Banjer21/DIY-HOTAS/Joystick/Righthanded Updated/Gimbal/Xaxis Arm V2 [B21] [ADD].stl

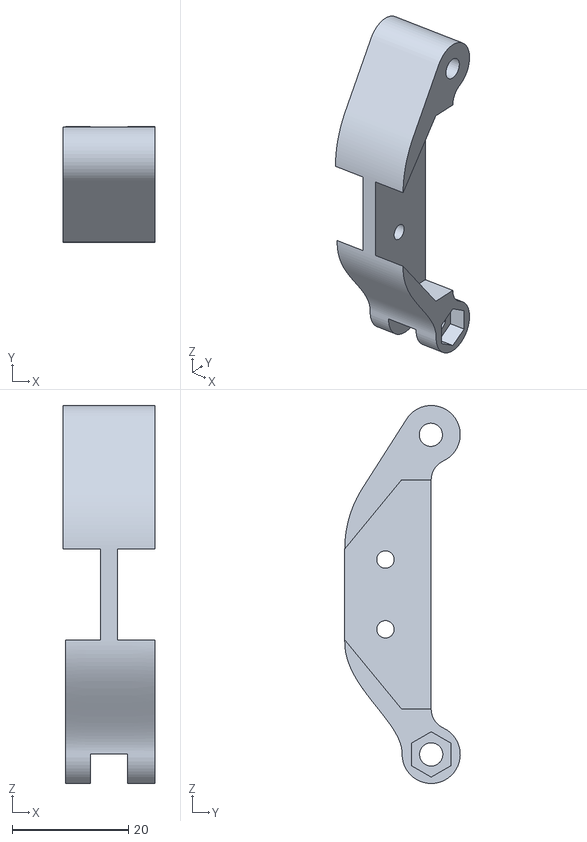
[picture p15: CAD file, 2025-05-15]
Joystick/Righthanded Updated/Gimbal/Xaxis Arm V2 [B21] [ADD].stl
15.8 x 19.9 x 65.0
