Banjer21/DIY-HOTAS/Joystick/Righthanded Updated/Head/Toggle Switch Housing V3 [B21] [ADD].stl

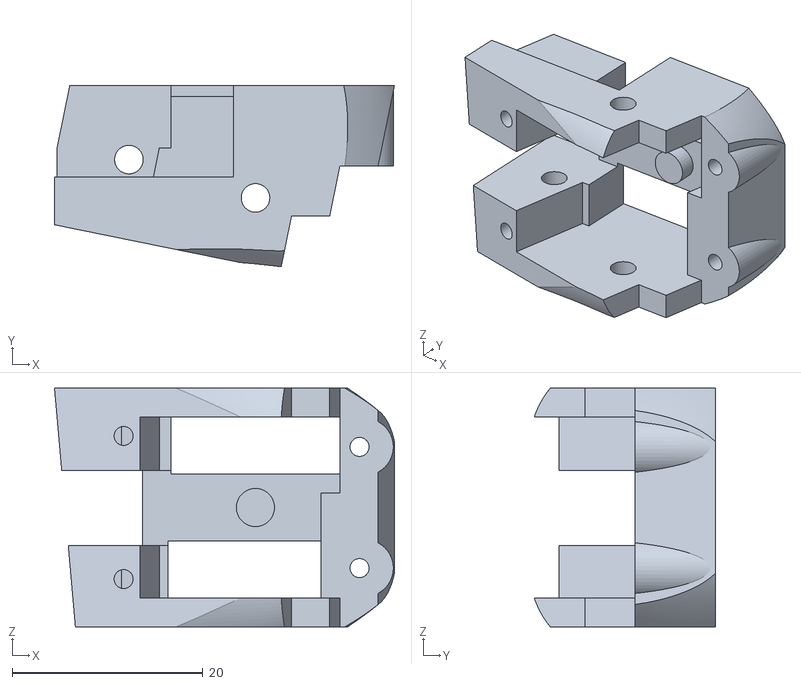
[picture p16: CAD file, 2025-05-15]
Joystick/Righthanded Updated/Head/Toggle Switch Housing V3 [B21] [ADD].stl
35.6 x 19.0 x 25.0
