Banjer21/DIY-HOTAS/Throttle/ThrottleBase Deskmount.step

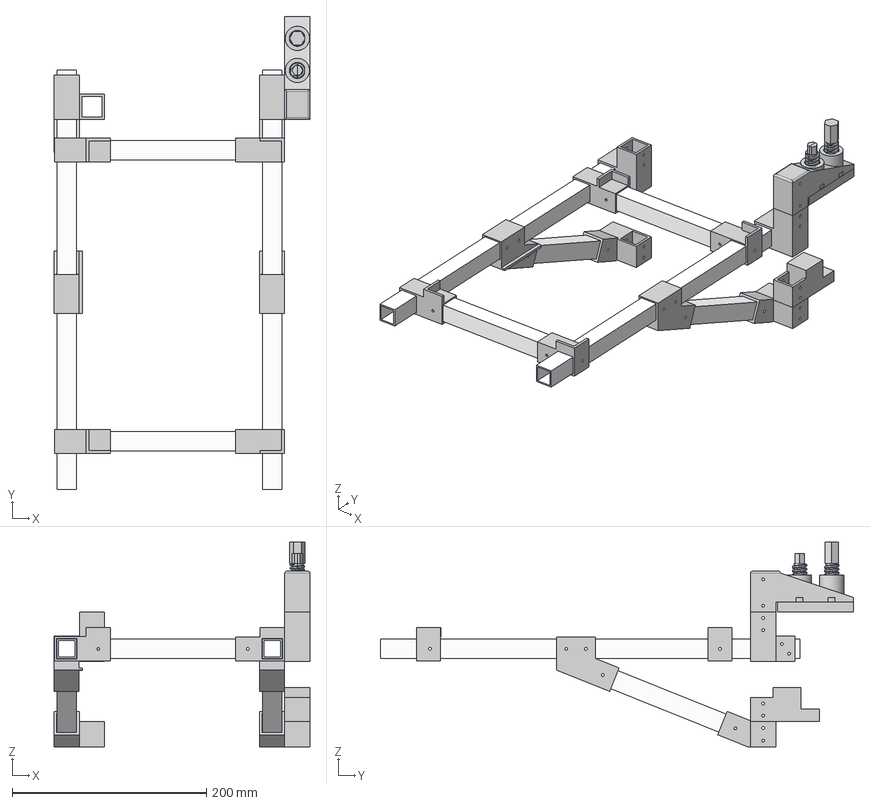
[picture p17: CAD file, 2025-04-23]
Throttle/ThrottleBase Deskmount.step
263.5 x 486.9 x 211.0 mm
