Banjer21/DIY-HOTAS/XY-stage.step

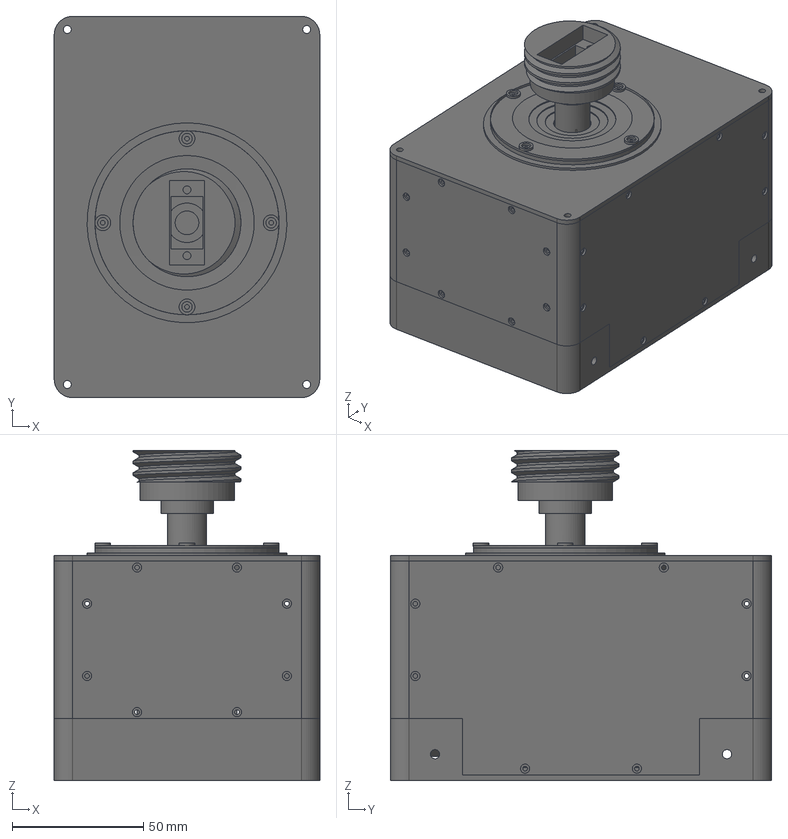
[picture p18: CAD file, 2025-02-13]
XY-stage.step
101.0 x 145.0 x 125.5 mm
Axle (2)
Xaxis resistive Right (1)
Xaxis Cariage Right (1)
MainFrame Right (1)
Yaxis resistive Right (1)
Case Right (1)
