Banjer21/DIY-HOTAS/Joystick/Righthanded joystick/Body/break lever.stl

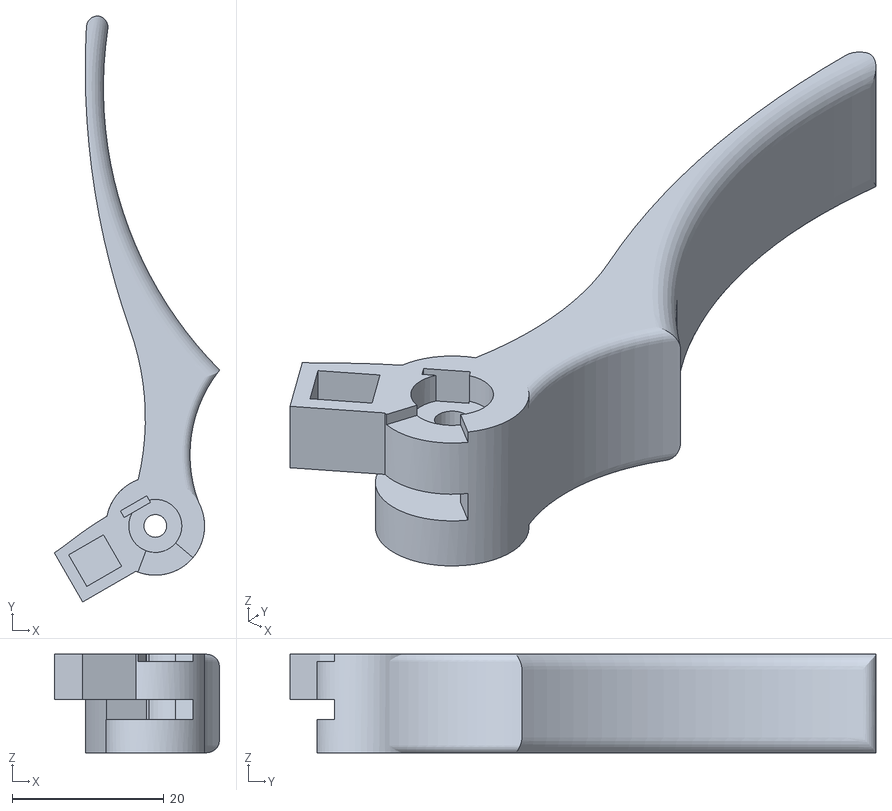
[picture p19: CAD file, 2025-03-08]
Joystick/Righthanded joystick/Body/break lever.stl
21.8 x 77.2 x 13.0
