Banjer21/DIY-HOTAS/Joystick/Righthanded joystick/Buttons/HS Top.stl

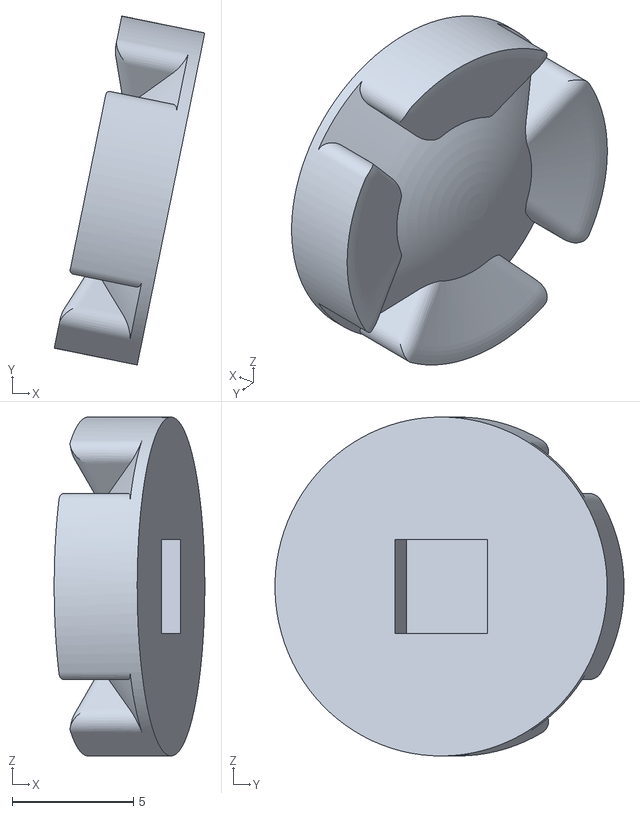
[picture p20: CAD file, 2025-03-08]
Joystick/Righthanded joystick/Buttons/HS Top.stl
6.22 x 14.4 x 14.0
