Banjer21/DIY-HOTAS/Joystick/Righthanded joystick/Gimbal/CoverPlate.stl

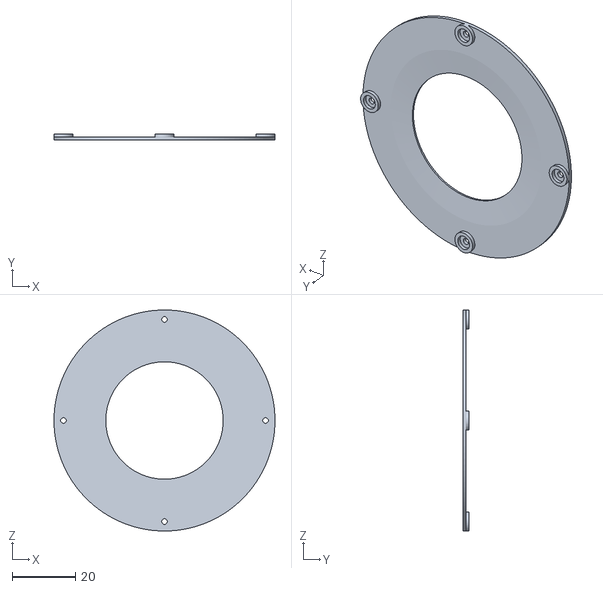
[picture p21: CAD file, 2025-03-08]
Joystick/Righthanded joystick/Gimbal/CoverPlate.stl
70.0 x 2.00 x 70.0
