Banjer21/DIY-HOTAS/Joystick/Righthanded joystick/Gimbal/GimbalCase/Lid.stl

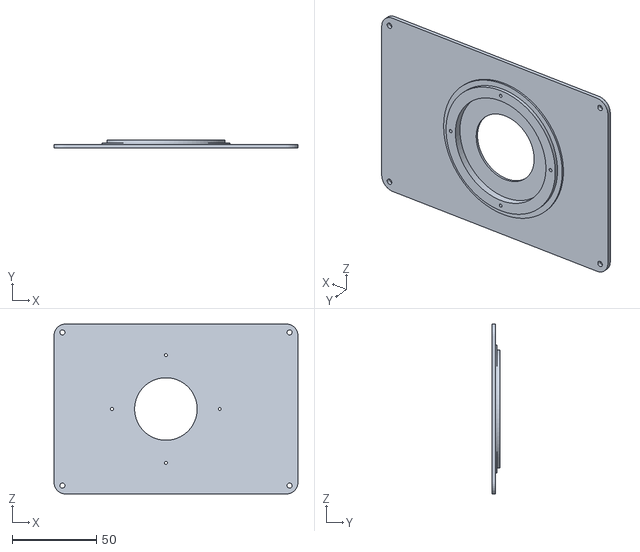
[picture p22: CAD file, 2025-03-08]
Joystick/Righthanded joystick/Gimbal/GimbalCase/Lid.stl
145.0 x 4.85 x 101.0
