Banjer21/DIY-HOTAS/Joystick/Righthanded joystick/Head/SecondTriggerHousing.stl

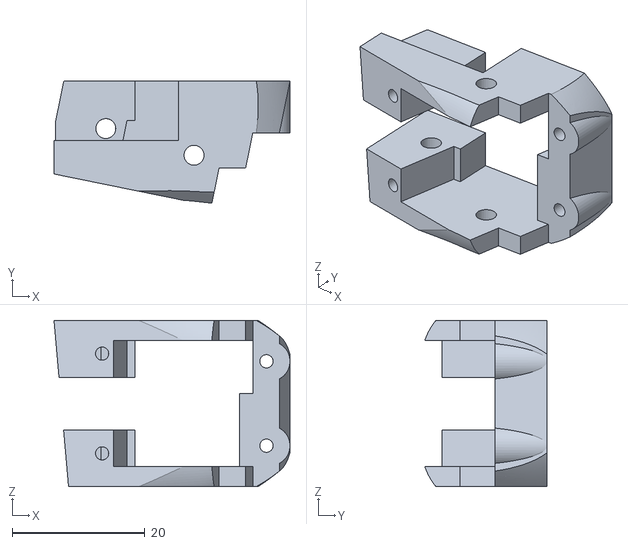
[picture p23: CAD file, 2025-03-08]
Joystick/Righthanded joystick/Head/SecondTriggerHousing.stl
35.5 x 18.4 x 25.0
