Banjer21/DIY-HOTAS/Joystick/Righthanded joystick/Zaxis/Zaxis topMag.stl

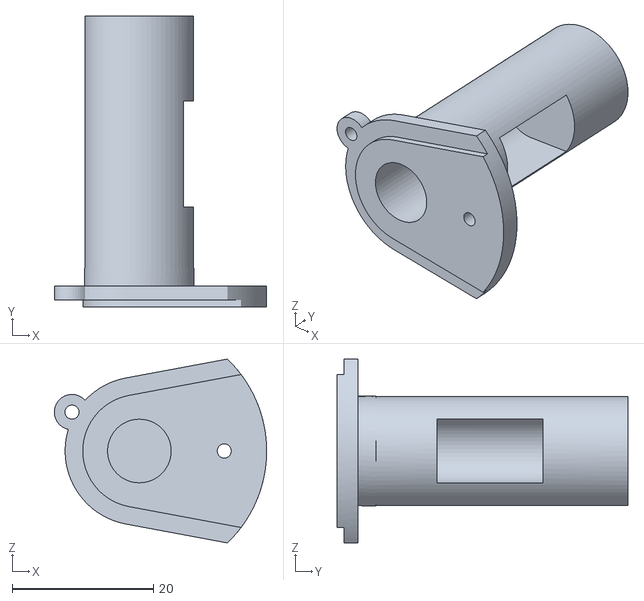
[picture p24: CAD file, 2025-03-08]
Joystick/Righthanded joystick/Zaxis/Zaxis topMag.stl
30.0 x 41.1 x 26.0
