Banjer21/DIY-HOTAS/Joystick/Righthanded Updated/Body/Brake Lever [B21] [ADD].stl

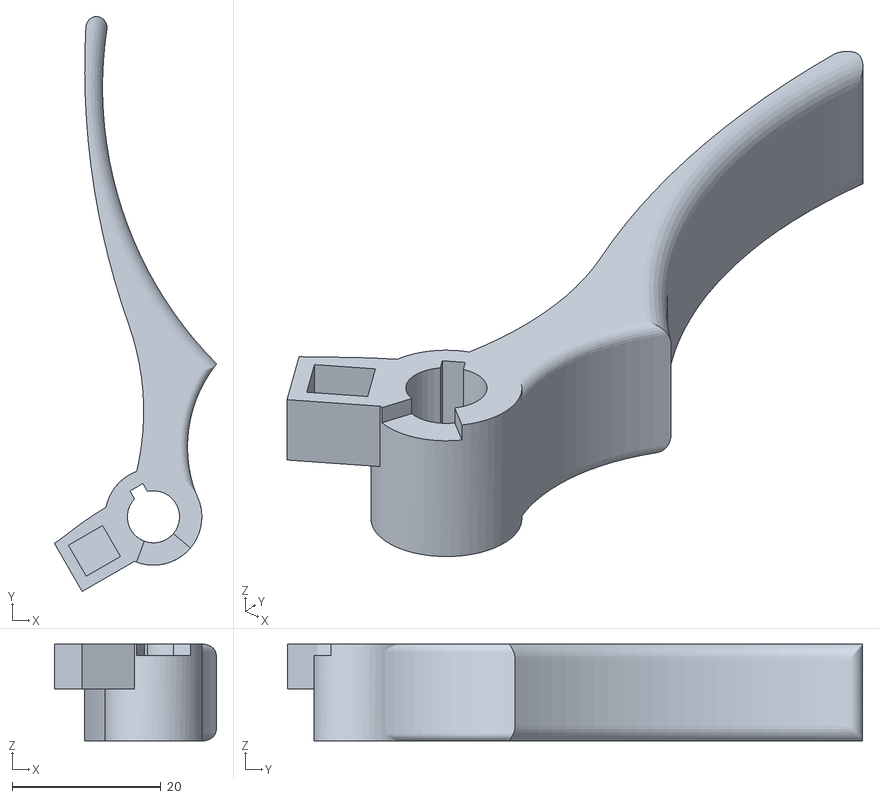
[picture p25: CAD file, 2025-05-15]
Joystick/Righthanded Updated/Body/Brake Lever [B21] [ADD].stl
21.8 x 77.2 x 13.0
