Banjer21/DIY-HOTAS/Joystick/Righthanded Updated/Head/Top Extended [B21].stl

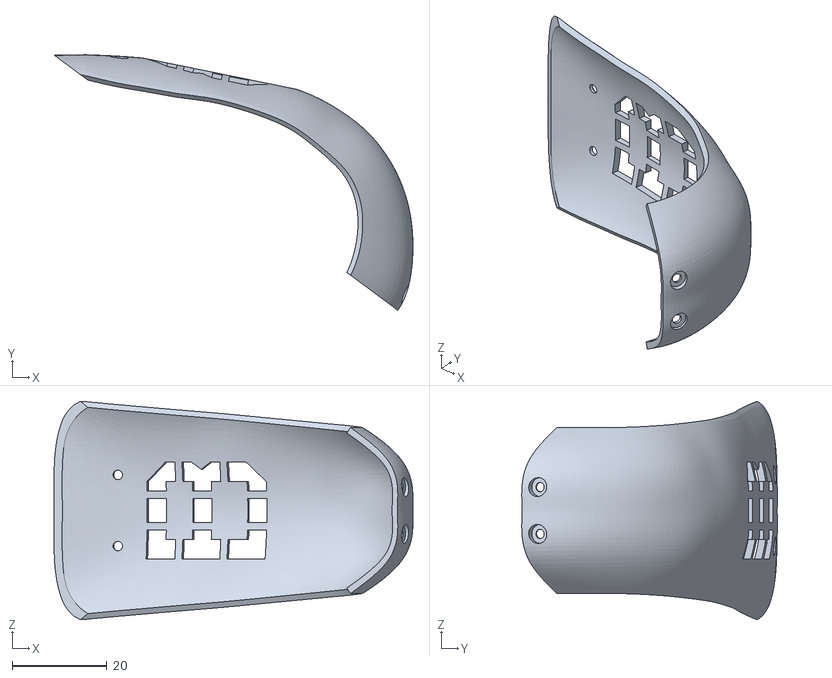
[picture p26: CAD file, 2025-05-15]
Joystick/Righthanded Updated/Head/Top Extended [B21].stl
75.7 x 53.9 x 46.1
