Banjer21/DIY-HOTAS/Joystick/Righthanded joystick/Buttons/Button.stl

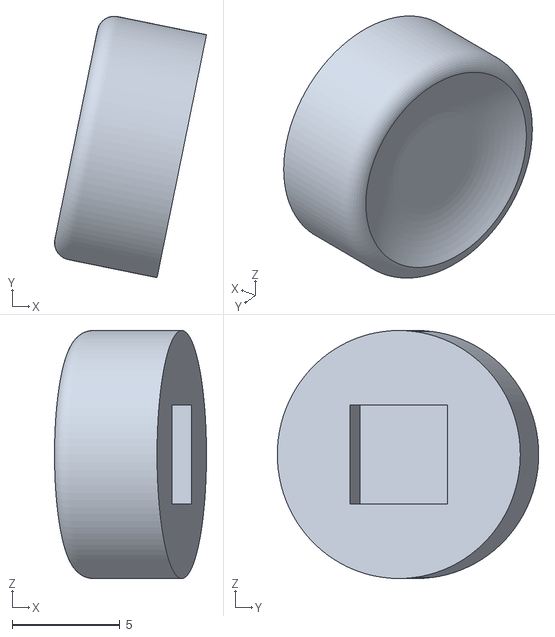
[picture p27: CAD file, 2025-03-08]
Joystick/Righthanded joystick/Buttons/Button.stl
7.05 x 12.1 x 11.5
