Banjer21/DIY-HOTAS/Joystick/Righthanded joystick/Gimbal/GimbalCase/BottomMCP.stl

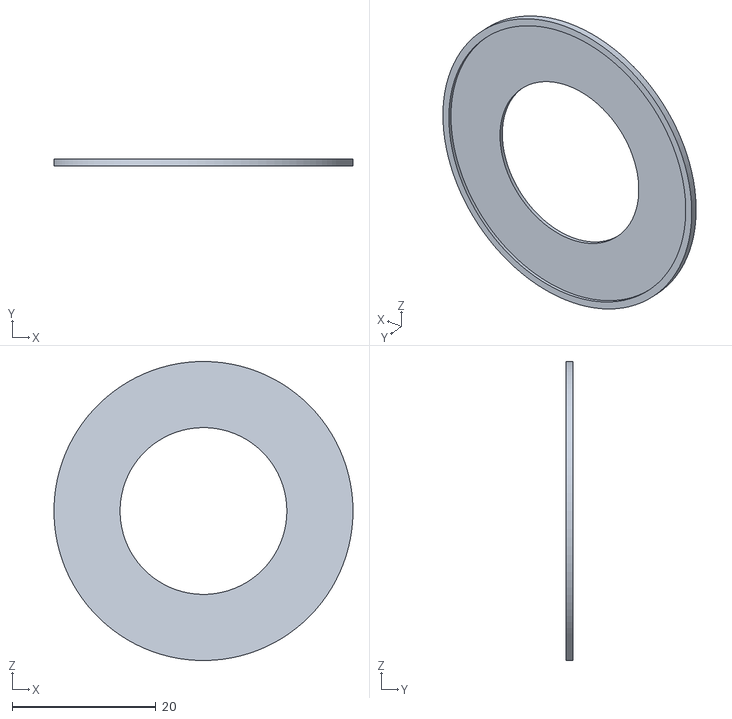
[picture p28: CAD file, 2025-03-08]
Joystick/Righthanded joystick/Gimbal/GimbalCase/BottomMCP.stl
41.6 x 0.95 x 41.6
