Banjer21/DIY-HOTAS/Joystick/Righthanded joystick/Head/Front Button Panel.stl

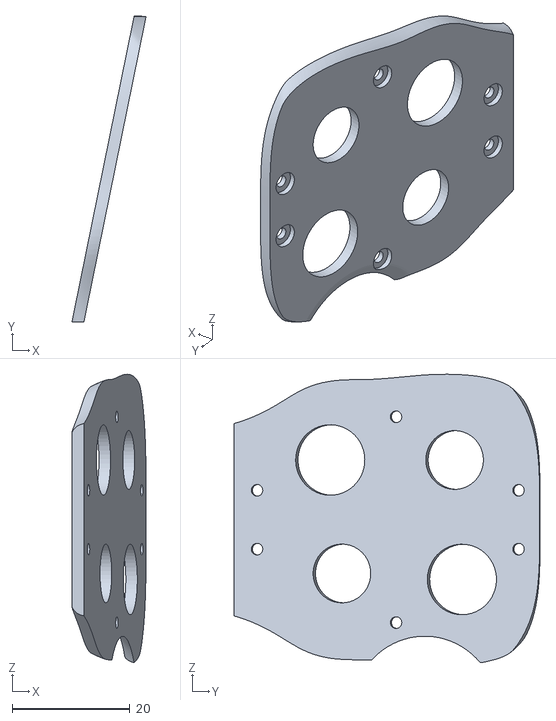
[picture p29: CAD file, 2025-03-08]
Joystick/Righthanded joystick/Head/Front Button Panel.stl
12.6 x 52.0 x 49.1
