Banjer21/DIY-HOTAS/Joystick/Righthanded Updated/Body/Thumb Hat 2 [ADD].stl

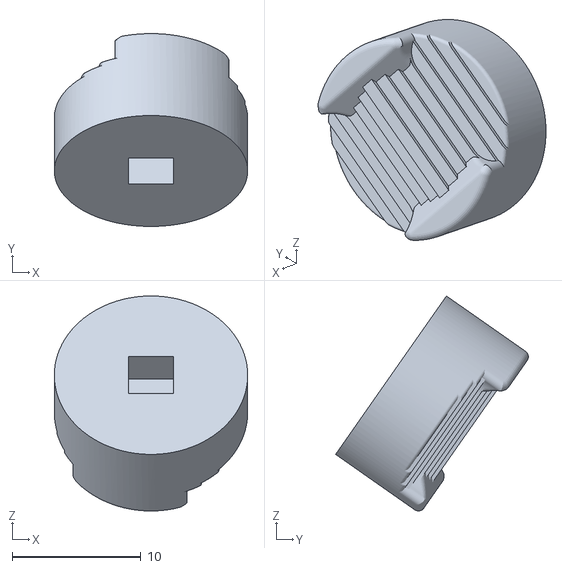
[picture p30: CAD file, 2025-05-15]
Joystick/Righthanded Updated/Body/Thumb Hat 2 [ADD].stl
15.0 x 15.0 x 16.7
