Banjer21/DIY-HOTAS/Joystick/Righthanded Updated/Head/HS Top 2.2 [B21].stl

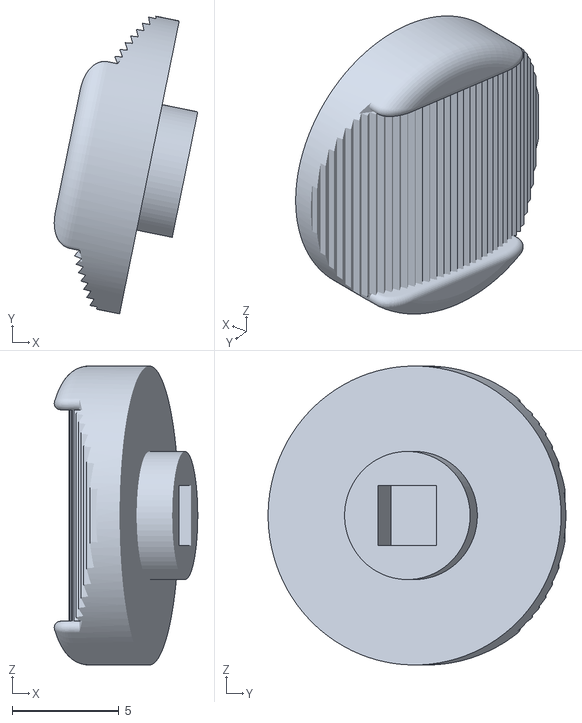
[picture p31: CAD file, 2025-05-15]
Joystick/Righthanded Updated/Head/HS Top 2.2 [B21].stl
6.72 x 13.9 x 14.0
