Banjer21/DIY-HOTAS/Joystick/Righthanded joystick/Buttons/JoyStickHead.stl

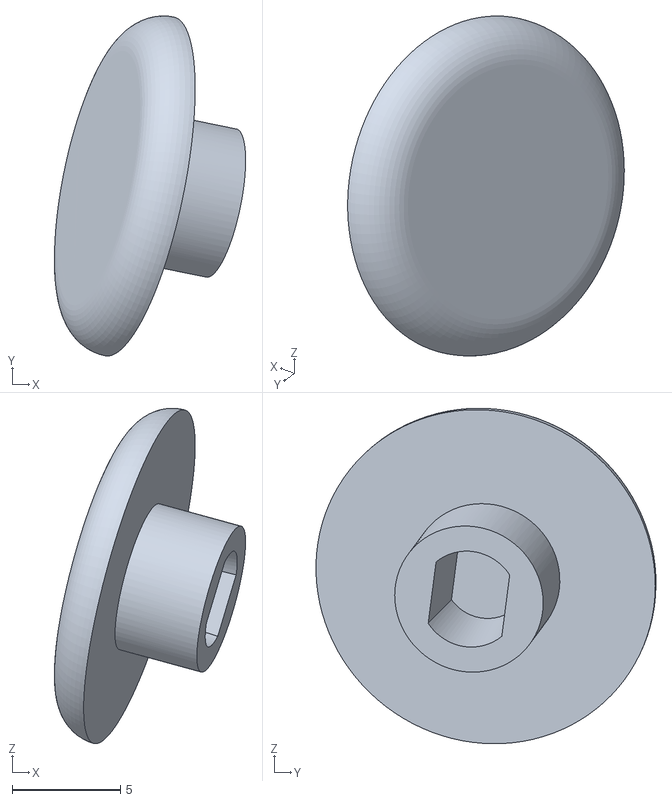
[picture p32: CAD file, 2025-03-08]
Joystick/Righthanded joystick/Buttons/JoyStickHead.stl
8.85 x 15.7 x 15.5
