Banjer21/DIY-HOTAS/Joystick/Righthanded joystick/Gimbal/GimbalCase/Case_Left.stl

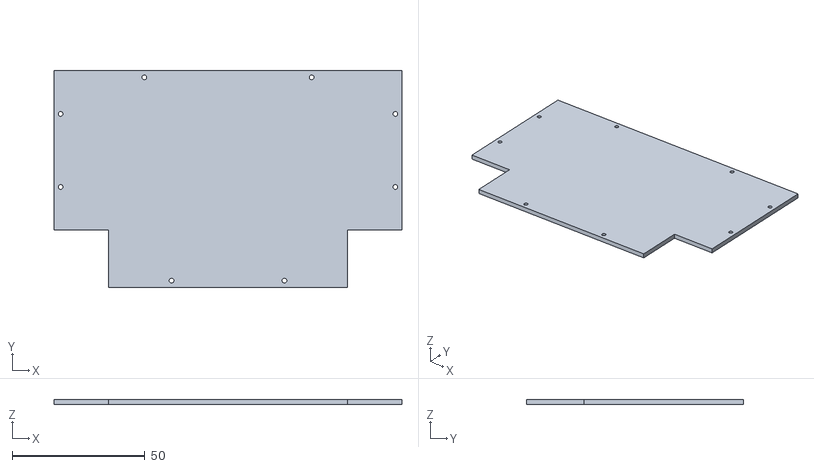
[picture p33: CAD file, 2025-03-08]
Joystick/Righthanded joystick/Gimbal/GimbalCase/Case_Left.stl
131.0 x 81.5 x 2.00
