Banjer21/DIY-HOTAS/Joystick/Righthanded joystick/Head/Left Panel JoyStick.stl

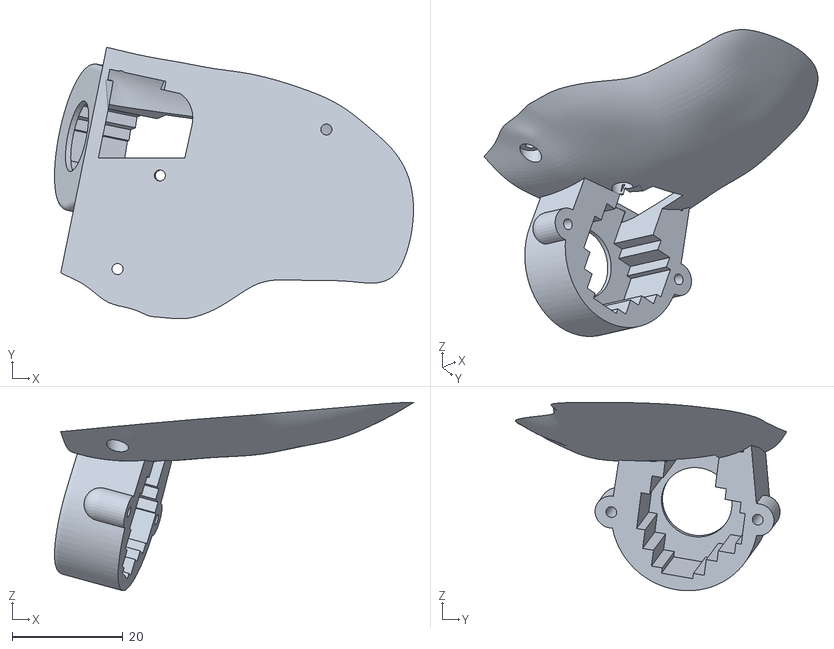
[picture p34: CAD file, 2025-03-08]
Joystick/Righthanded joystick/Head/Left Panel JoyStick.stl
64.9 x 49.1 x 34.1
