Banjer21/DIY-HOTAS/Joystick/Righthanded joystick/Zaxis/BearingHolder.stl

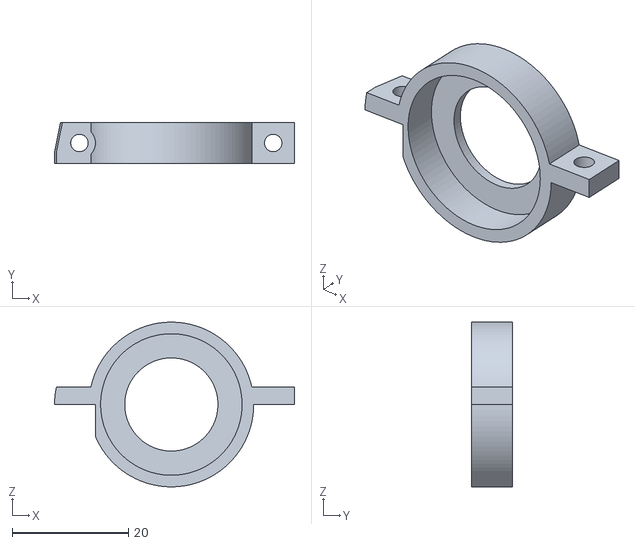
[picture p35: CAD file, 2025-03-08]
Joystick/Righthanded joystick/Zaxis/BearingHolder.stl
41.2 x 7.00 x 28.3
