Banjer21/DIY-HOTAS/Joystick/Righthanded Updated/Body/PinkyButton [B21] [ADD].stl

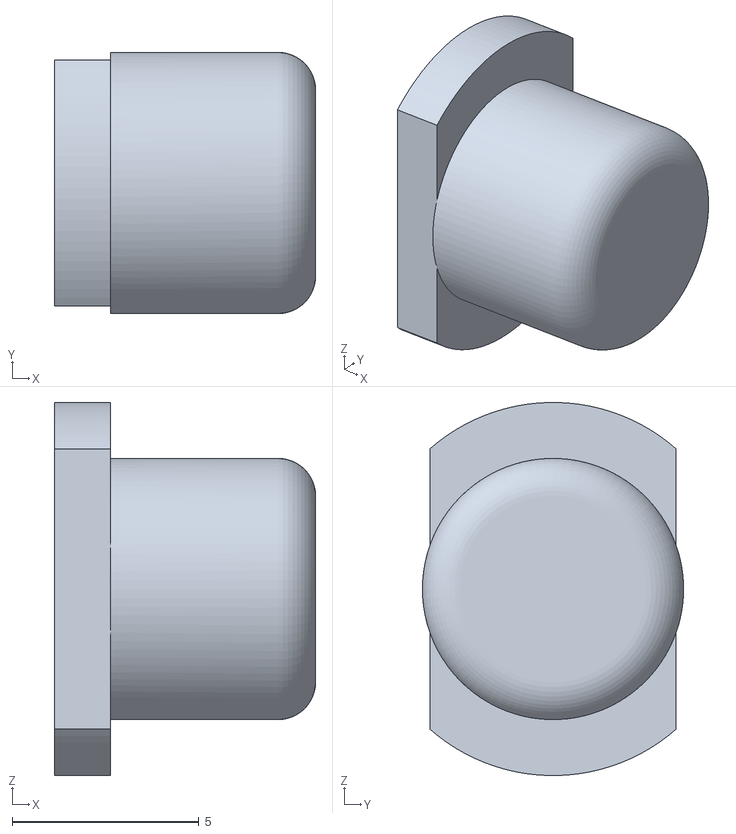
[picture p36: CAD file, 2025-05-15]
Joystick/Righthanded Updated/Body/PinkyButton [B21] [ADD].stl
7.00 x 7.00 x 10.00
