Banjer21/DIY-HOTAS/Joystick/Righthanded Updated/Gimbal/GimbalCase/Lid [B21] [ADD].stl

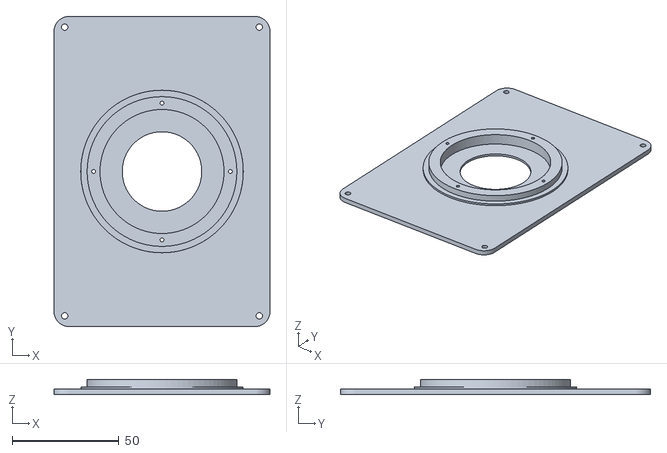
[picture p37: CAD file, 2025-05-15]
Joystick/Righthanded Updated/Gimbal/GimbalCase/Lid [B21] [ADD].stl
101.0 x 145.0 x 6.85
