Banjer21/DIY-HOTAS/Joystick/Righthanded Updated/Gimbal/Xaxis Cariage V2 [B21] [ADD].stl

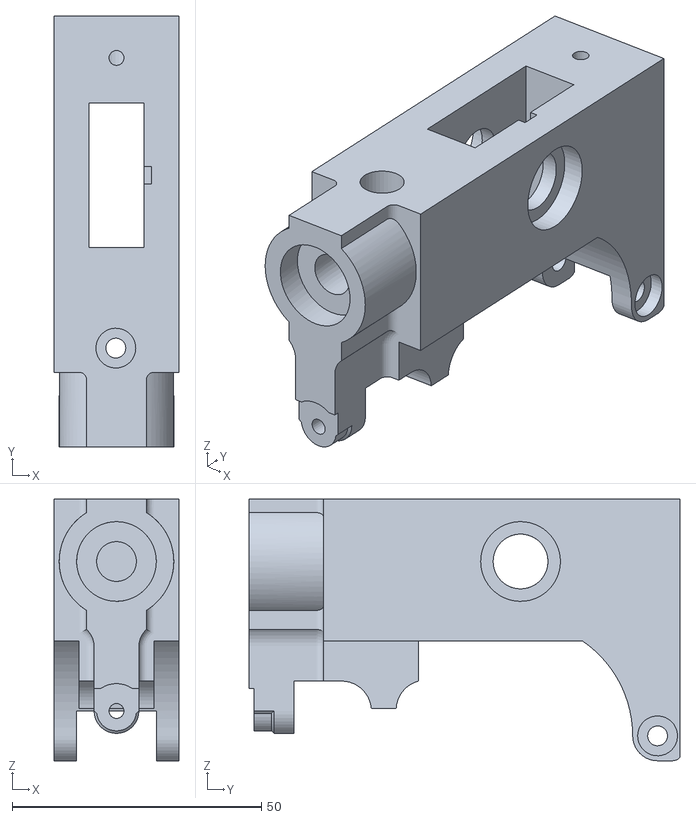
[picture p38: CAD file, 2025-05-15]
Joystick/Righthanded Updated/Gimbal/Xaxis Cariage V2 [B21] [ADD].stl
25.0 x 86.5 x 52.5
