Banjer21/DIY-HOTAS/Joystick/Righthanded Updated/Head/HS Top [B21].stl

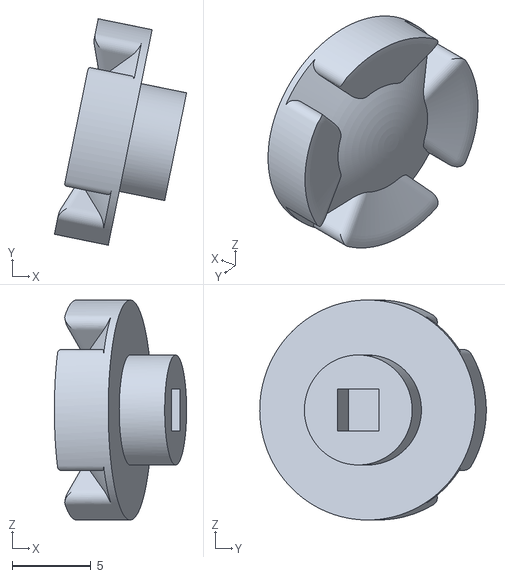
[picture p39: CAD file, 2025-05-15]
Joystick/Righthanded Updated/Head/HS Top [B21].stl
8.41 x 14.4 x 14.0
