Banjer21/DIY-HOTAS/Joystick/Righthanded joystick/Body/handsupport.stl

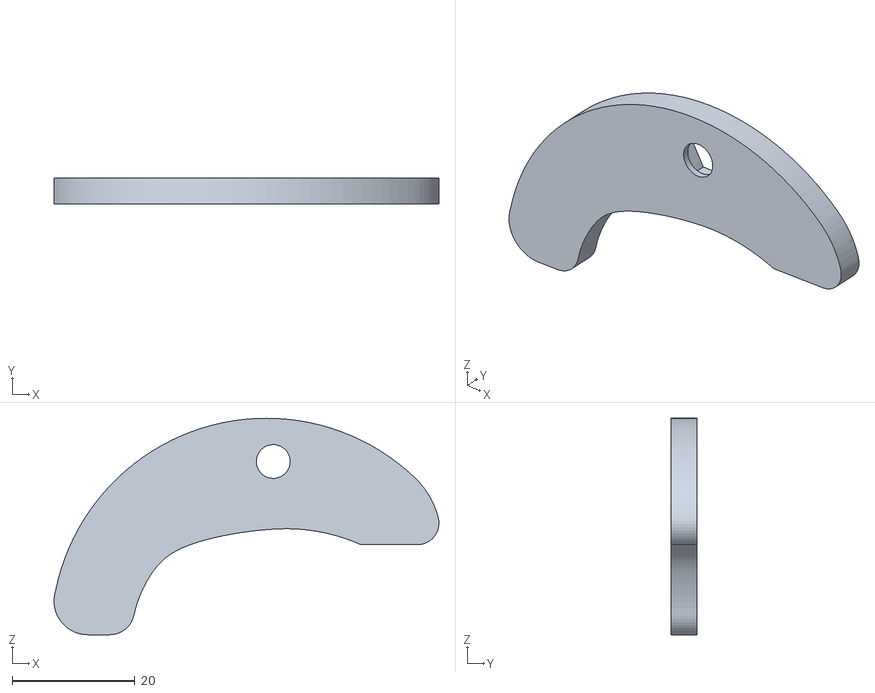
[picture p40: CAD file, 2025-03-08]
Joystick/Righthanded joystick/Body/handsupport.stl
62.6 x 4.30 x 35.2
