Banjer21/DIY-HOTAS/Joystick/Righthanded joystick/Buttons/PinkyButton.stl

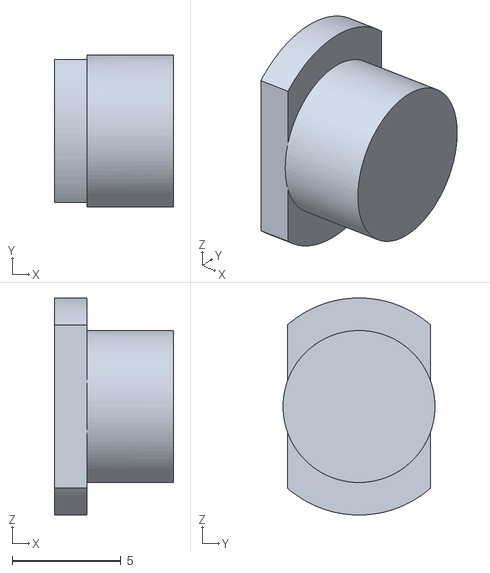
[picture p41: CAD file, 2025-03-08]
Joystick/Righthanded joystick/Buttons/PinkyButton.stl
5.50 x 7.00 x 10.00
