Banjer21/DIY-HOTAS/Joystick/Righthanded joystick/Gimbal/GimbalCase/Case_Upper.stl

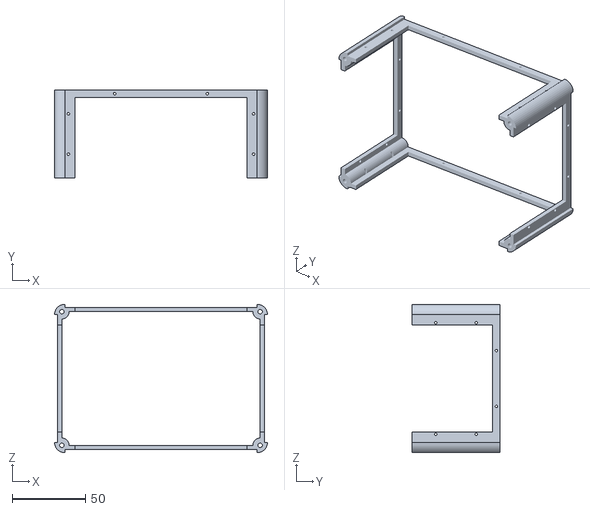
[picture p42: CAD file, 2025-03-08]
Joystick/Righthanded joystick/Gimbal/GimbalCase/Case_Upper.stl
145.0 x 60.0 x 101.0
