Banjer21/DIY-HOTAS/Joystick/Righthanded joystick/Head/Primary Trigger.stl

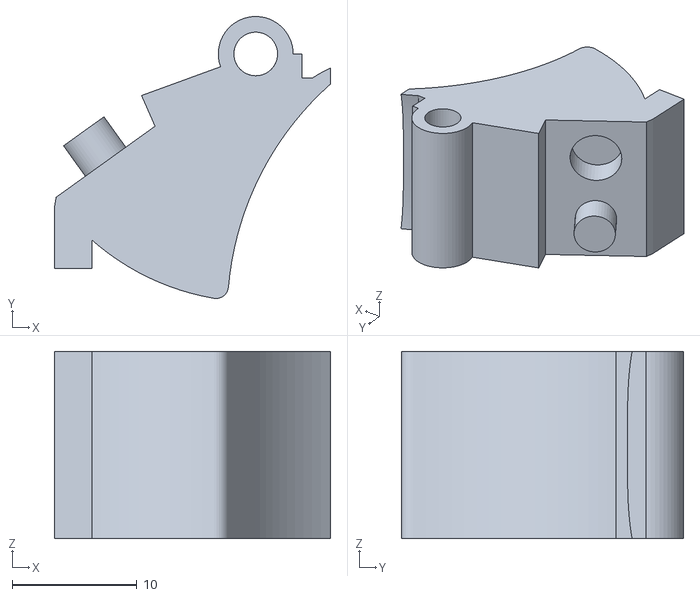
[picture p43: CAD file, 2025-03-08]
Joystick/Righthanded joystick/Head/Primary Trigger.stl
22.1 x 22.6 x 15.0
