Banjer21/DIY-HOTAS/Joystick/Righthanded joystick/Zaxis/Bearing HallEffect.stl

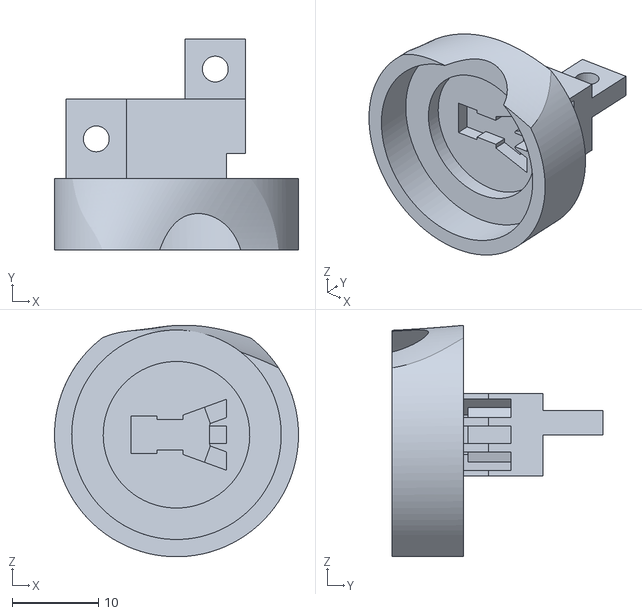
[picture p44: CAD file, 2025-03-08]
Joystick/Righthanded joystick/Zaxis/Bearing HallEffect.stl
28.3 x 24.5 x 26.8
