Banjer21/DIY-HOTAS/Joystick/Righthanded Updated/Body/Thumb Hat 1 [ADD].stl

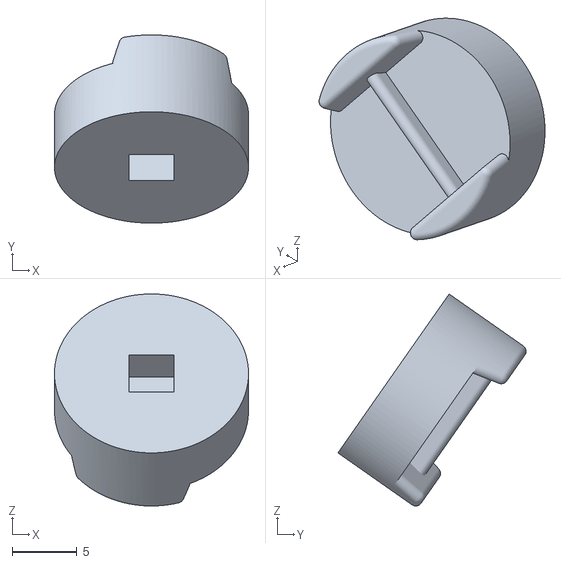
[picture p45: CAD file, 2025-05-15]
Joystick/Righthanded Updated/Body/Thumb Hat 1 [ADD].stl
15.0 x 14.5 x 16.4
