Banjer21/DIY-HOTAS/Joystick/Righthanded Updated/Gimbal/GimbalCase/Smol Ring [B21] [ADD].stl

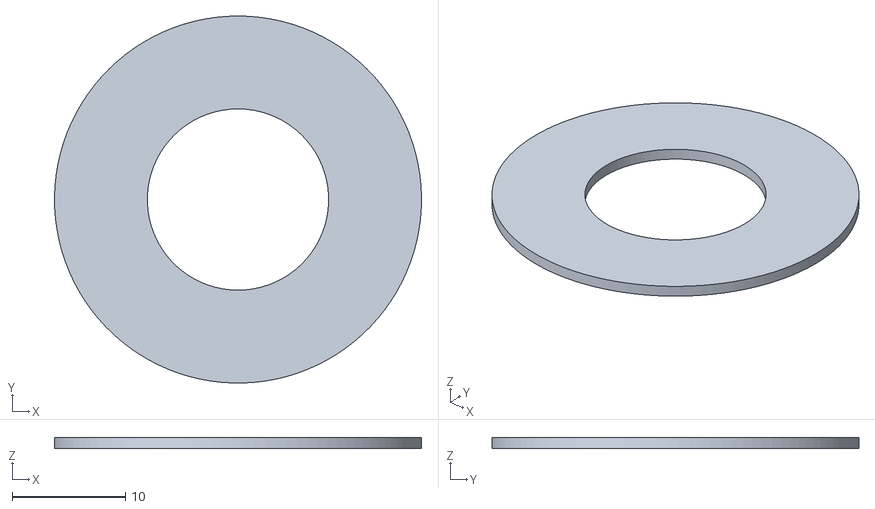
[picture p46: CAD file, 2025-05-15]
Joystick/Righthanded Updated/Gimbal/GimbalCase/Smol Ring [B21] [ADD].stl
32.4 x 32.4 x 1.00
