Banjer21/DIY-HOTAS/Joystick/Righthanded Updated/Head/JoyStick Housing Back [B21].stl

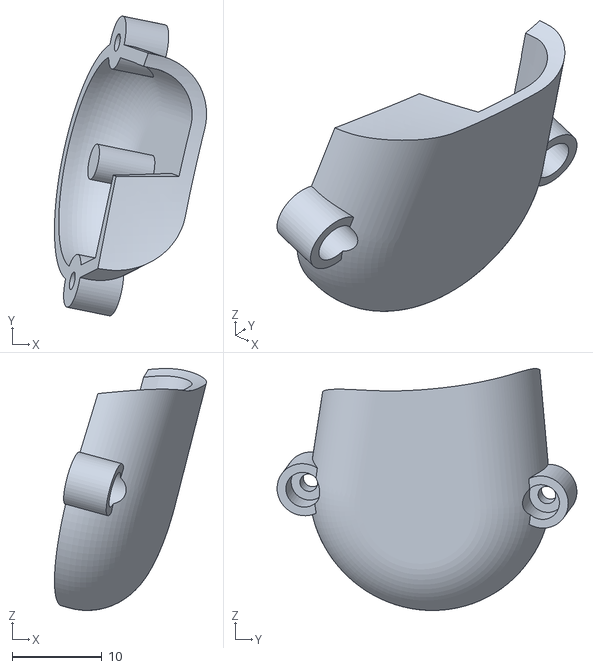
[picture p47: CAD file, 2025-05-15]
Joystick/Righthanded Updated/Head/JoyStick Housing Back [B21].stl
16.9 x 33.3 x 26.9
