Banjer21/DIY-HOTAS/Joystick/Righthanded joystick/Gimbal/GimbalCase/SCP.stl

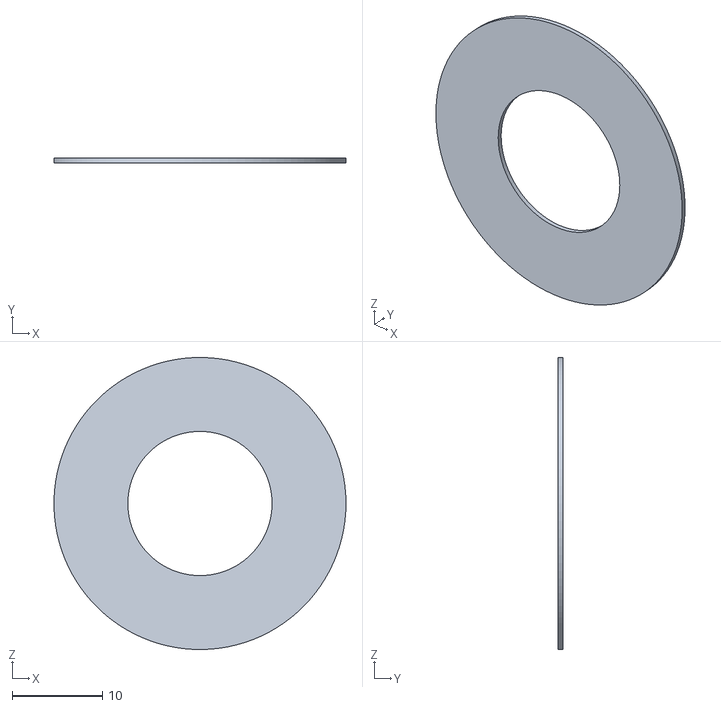
[picture p48: CAD file, 2025-03-08]
Joystick/Righthanded joystick/Gimbal/GimbalCase/SCP.stl
32.4 x 0.5 x 32.4
