Banjer21/DIY-HOTAS/Joystick/Righthanded joystick/Head/SecondTrigger.stl

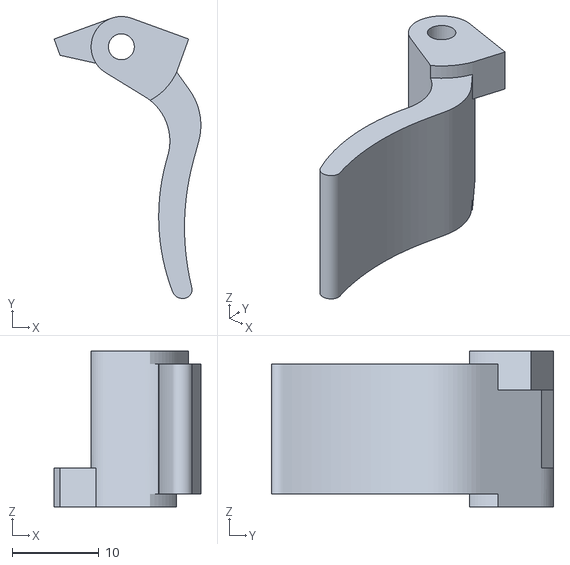
[picture p49: CAD file, 2025-03-08]
Joystick/Righthanded joystick/Head/SecondTrigger.stl
17.0 x 32.6 x 18.0
