Banjer21/DIY-HOTAS/Joystick/Righthanded joystick/Zaxis/Zaxis Connector bottom.stl

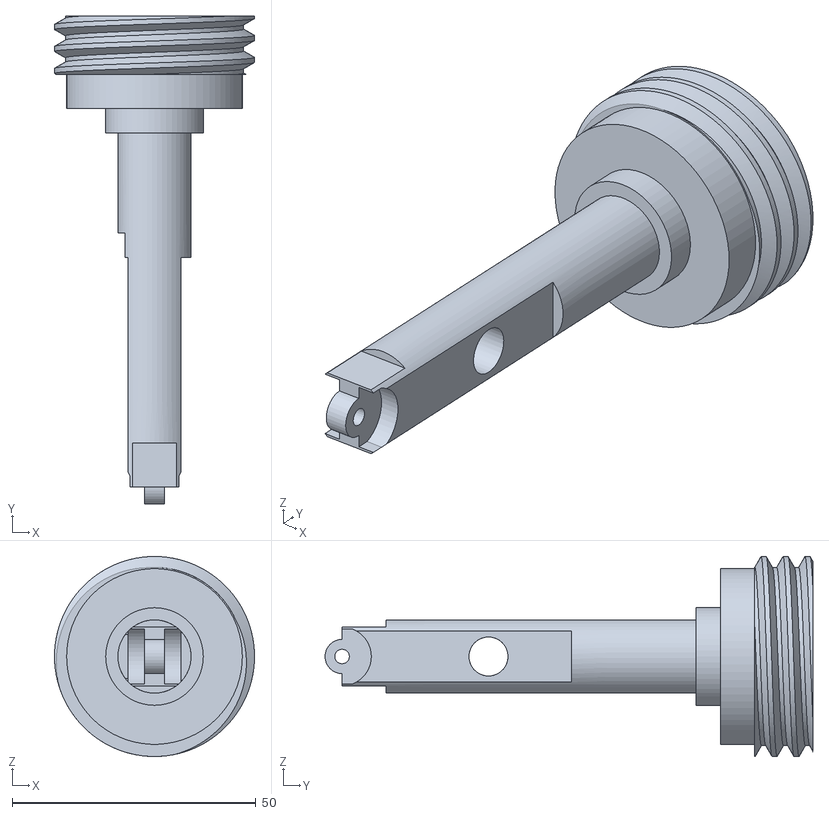
[picture p50: CAD file, 2025-03-08]
Joystick/Righthanded joystick/Zaxis/Zaxis Connector bottom.stl
41.0 x 100.0 x 41.0
