Banjer21/DIY-HOTAS/Joystick/Righthanded Updated/Body/Momentary Trigger [B21 [ADD].stl

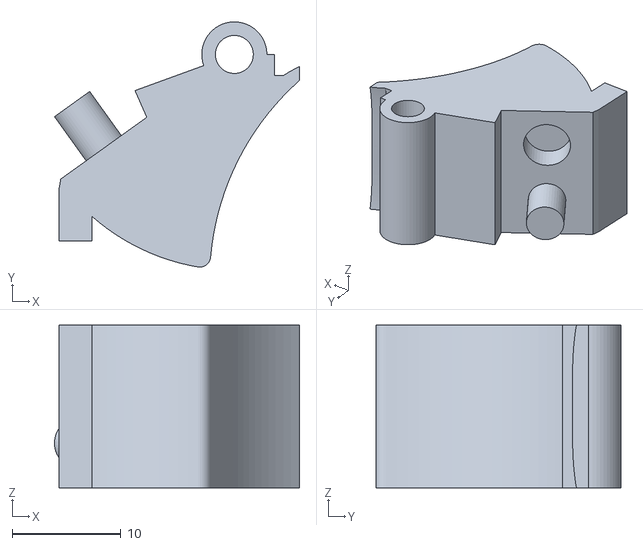
[picture p51: CAD file, 2025-05-15]
Joystick/Righthanded Updated/Body/Momentary Trigger [B21 [ADD].stl
22.6 x 22.6 x 15.0
