Banjer21/DIY-HOTAS/Joystick/Righthanded Updated/Gimbal/Y Cam V2 [B21] [ADD].stl

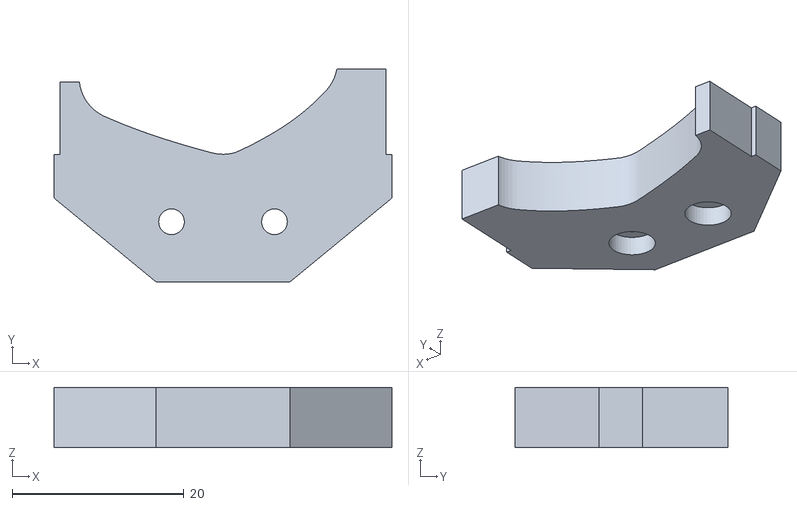
[picture p52: CAD file, 2025-05-15]
Joystick/Righthanded Updated/Gimbal/Y Cam V2 [B21] [ADD].stl
39.4 x 24.8 x 7.00
