Banjer21/DIY-HOTAS/Joystick/Righthanded Updated/Head/Top Short [B21].stl

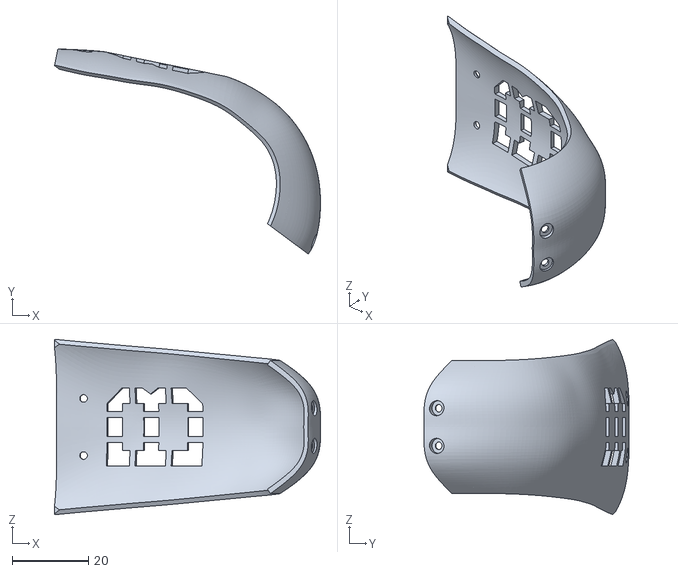
[picture p53: CAD file, 2025-05-15]
Joystick/Righthanded Updated/Head/Top Short [B21].stl
69.9 x 53.9 x 46.0
