Banjer21/DIY-HOTAS/Joystick/Righthanded Updated/Gimbal/GimbalCase/Case Lower [B21] [ADD].stl

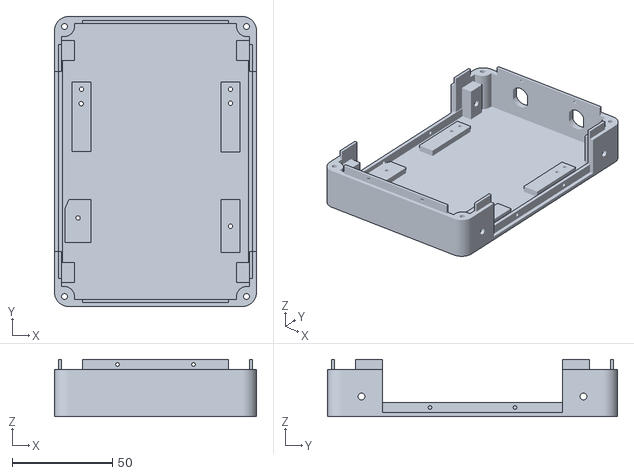
[picture p54: CAD file, 2025-05-15]
Joystick/Righthanded Updated/Gimbal/GimbalCase/Case Lower [B21] [ADD].stl
101.0 x 145.0 x 28.5
