Banjer21/DIY-HOTAS/Joystick/Righthanded Updated/Gimbal/X-Y Connector V2 [B21} [ADD}.stl

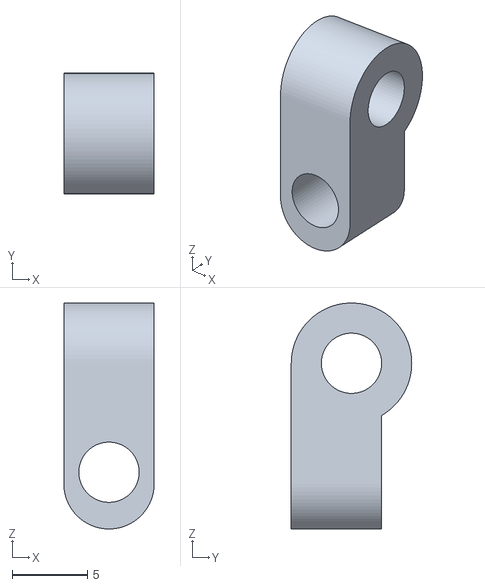
[picture p55: CAD file, 2025-05-15]
Joystick/Righthanded Updated/Gimbal/X-Y Connector V2 [B21} [ADD}.stl
6.00 x 8.00 x 15.0
