Banjer21/DIY-HOTAS/Joystick/Righthanded Updated/Head/Left Panel JoyStick [B21] [ADD].stl

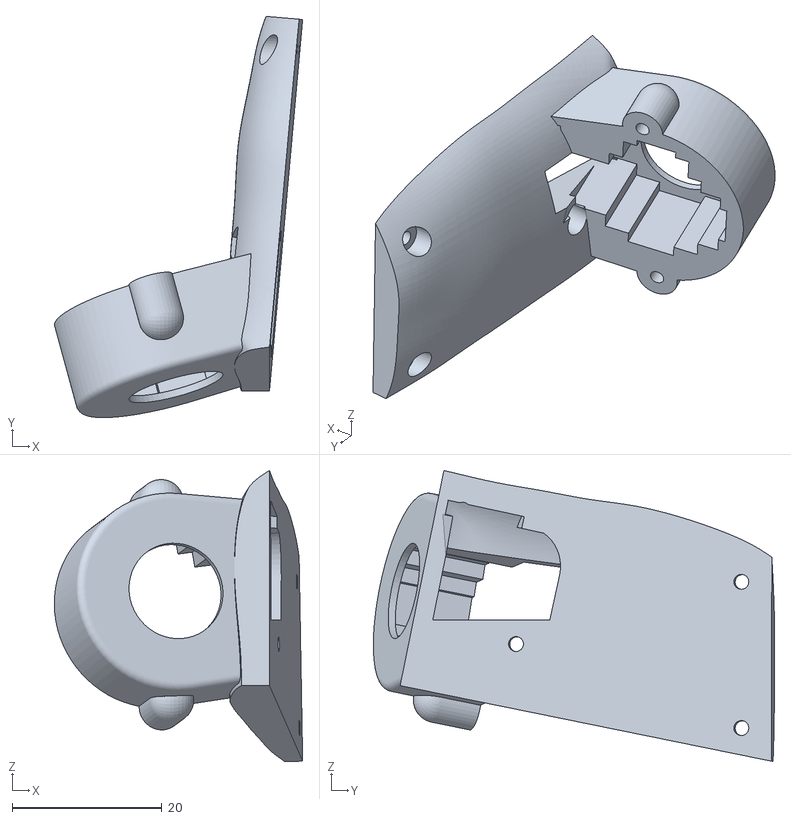
[picture p56: CAD file, 2025-05-15]
Joystick/Righthanded Updated/Head/Left Panel JoyStick [B21] [ADD].stl
33.2 x 53.6 x 38.9
