Banjer21/DIY-HOTAS/Joystick/Righthanded joystick/Gimbal/XaxisCamholder.stl

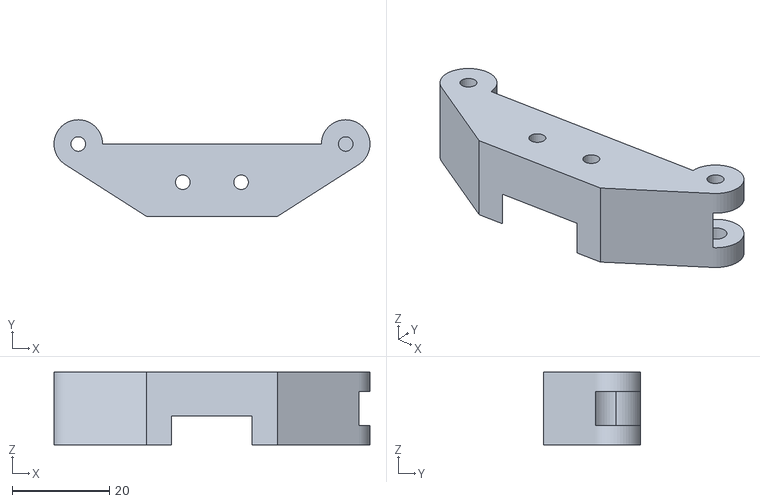
[picture p57: CAD file, 2025-03-08]
Joystick/Righthanded joystick/Gimbal/XaxisCamholder.stl
65.0 x 19.9 x 15.0
