Banjer21/DIY-HOTAS/Joystick/Righthanded joystick/Head/Left Side.stl

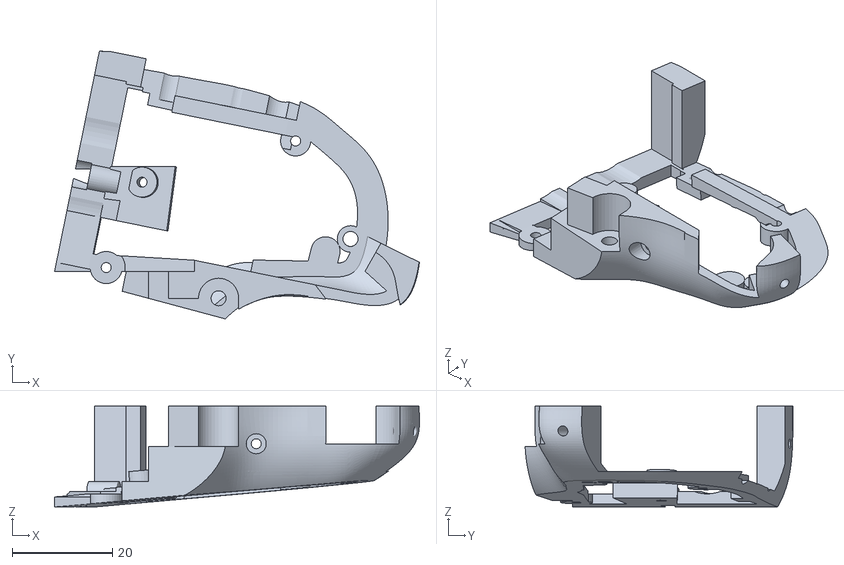
[picture p58: CAD file, 2025-03-08]
Joystick/Righthanded joystick/Head/Left Side.stl
72.8 x 53.4 x 20.1
