Banjer21/DIY-HOTAS/Joystick/Righthanded Updated/Gimbal/GimbalCase/Medium ring [B21] [ADD].stl

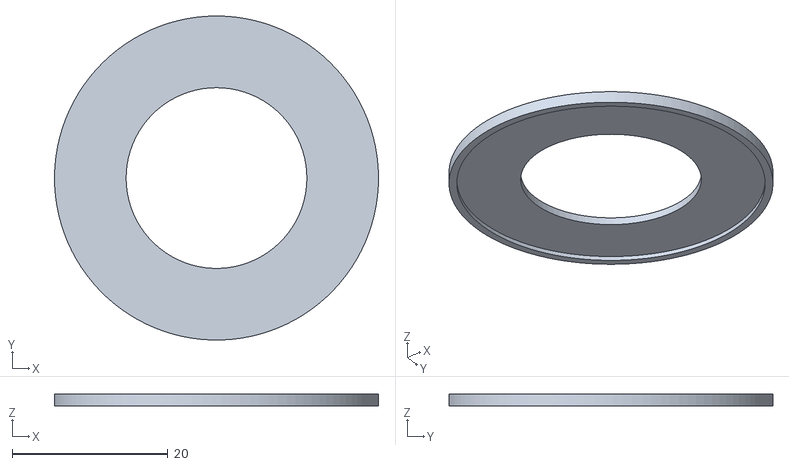
[picture p59: CAD file, 2025-05-15]
Joystick/Righthanded Updated/Gimbal/GimbalCase/Medium ring [B21] [ADD].stl
41.6 x 41.6 x 1.58
