Banjer21/DIY-HOTAS/Joystick/Righthanded joystick/Gimbal/CamHolderSpringConnector.stl

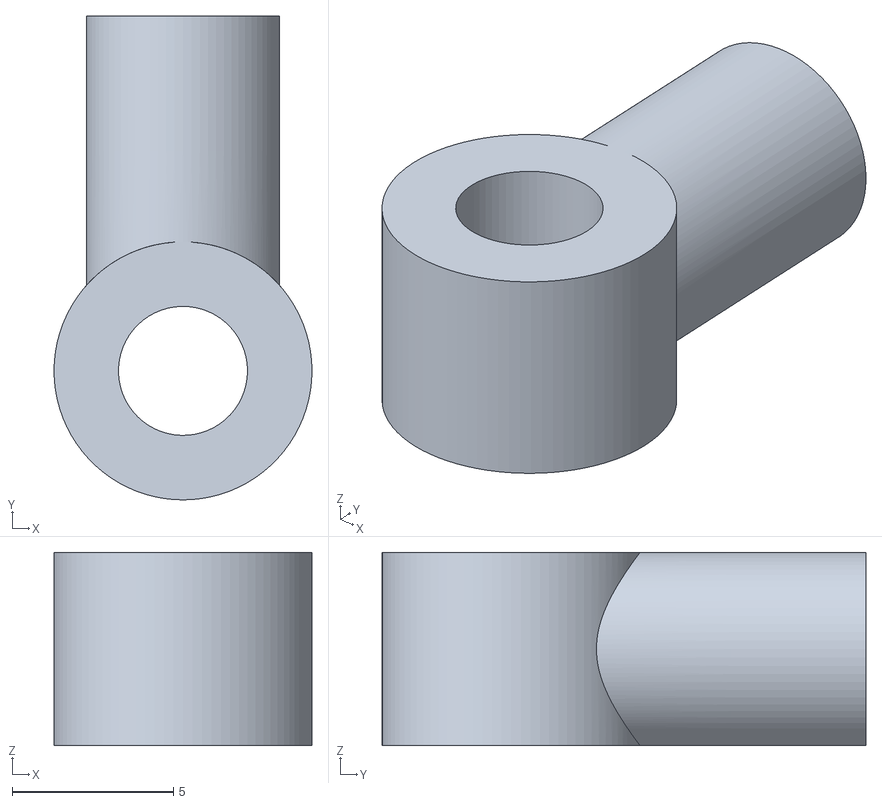
[picture p60: CAD file, 2025-03-08]
Joystick/Righthanded joystick/Gimbal/CamHolderSpringConnector.stl
8.00 x 15.0 x 6.00
