Banjer21/DIY-HOTAS/Joystick/Righthanded joystick/Gimbal/GimbalCase/BottomLCP.stl

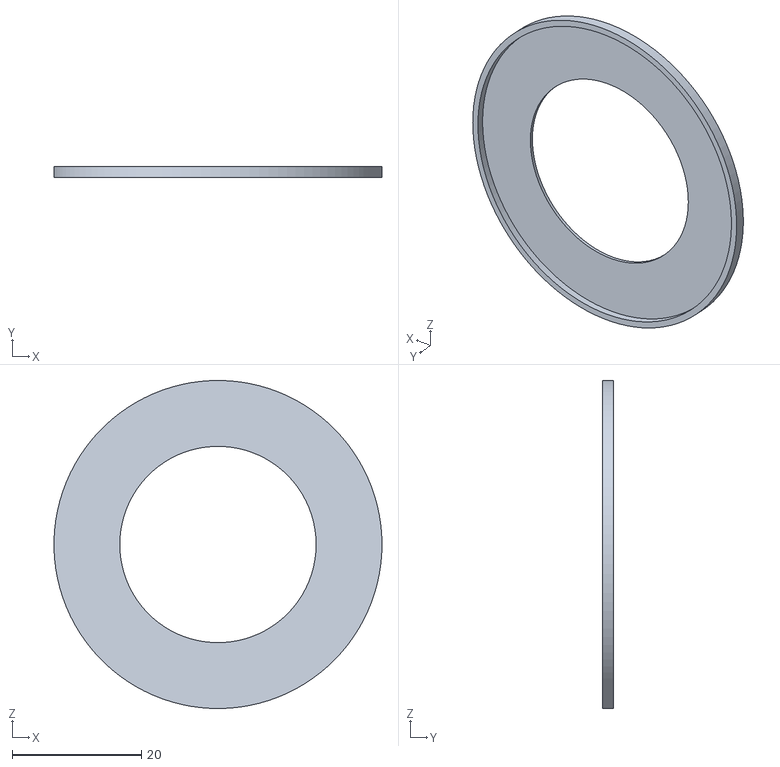
[picture p61: CAD file, 2025-03-08]
Joystick/Righthanded joystick/Gimbal/GimbalCase/BottomLCP.stl
50.8 x 1.65 x 50.8
