Banjer21/DIY-HOTAS/Joystick/Righthanded joystick/Head/Right Side.stl

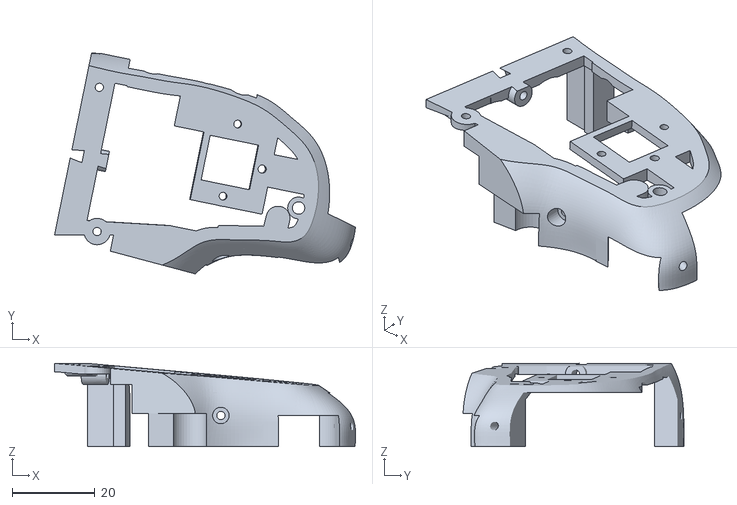
[picture p62: CAD file, 2025-03-08]
Joystick/Righthanded joystick/Head/Right Side.stl
72.8 x 53.4 x 20.1
