Banjer21/DIY-HOTAS/Joystick/Righthanded Updated/Gimbal/Gimbal Shaft [B21] [ADD].stl

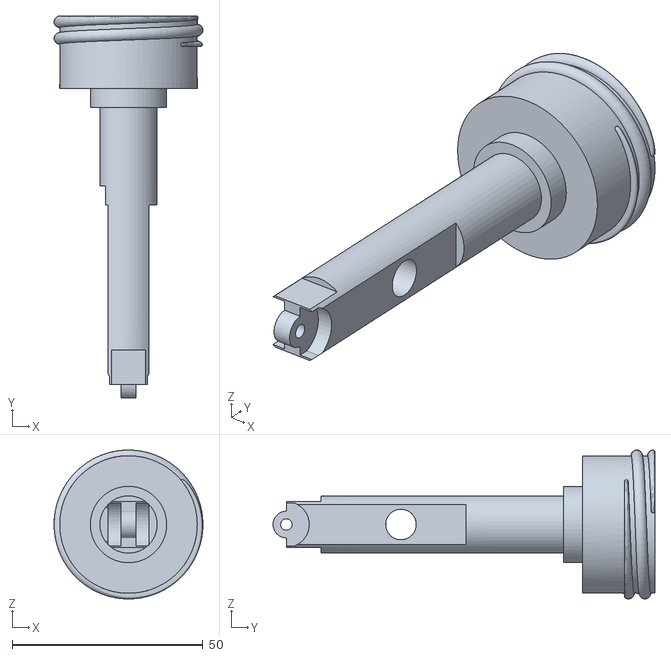
[picture p63: CAD file, 2025-05-15]
Joystick/Righthanded Updated/Gimbal/Gimbal Shaft [B21] [ADD].stl
39.0 x 100.0 x 39.0
