Banjer21/DIY-HOTAS/Joystick/Righthanded Updated/Gimbal/GimbalCase/Case Left [B21] [ADD].stl

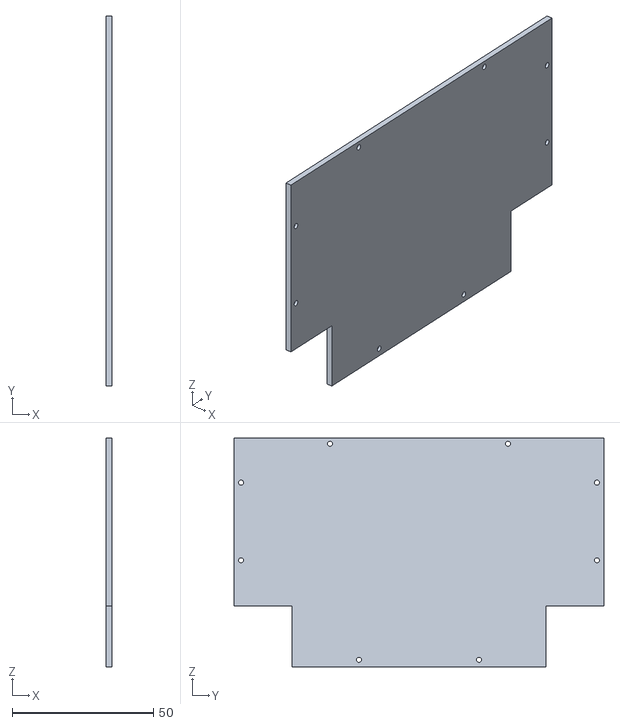
[picture p64: CAD file, 2025-05-15]
Joystick/Righthanded Updated/Gimbal/GimbalCase/Case Left [B21] [ADD].stl
2.00 x 131.0 x 81.0
