Banjer21/DIY-HOTAS/Joystick/Righthanded joystick/Gimbal/Xaxis Cariage.stl

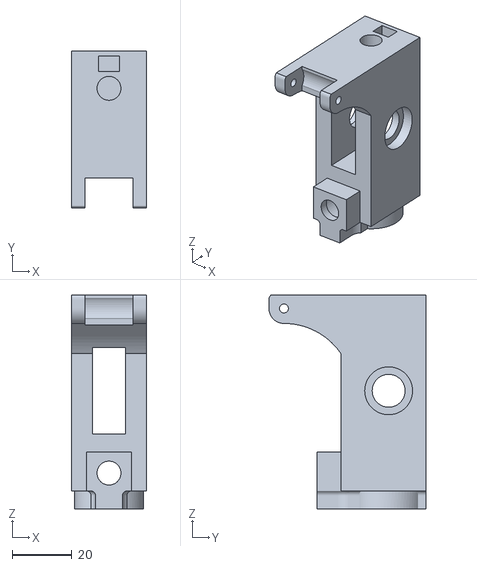
[picture p65: CAD file, 2025-03-08]
Joystick/Righthanded joystick/Gimbal/Xaxis Cariage.stl
25.0 x 52.5 x 71.5
