Banjer21/DIY-HOTAS/Joystick/Righthanded joystick/Head/PCB holder.stl

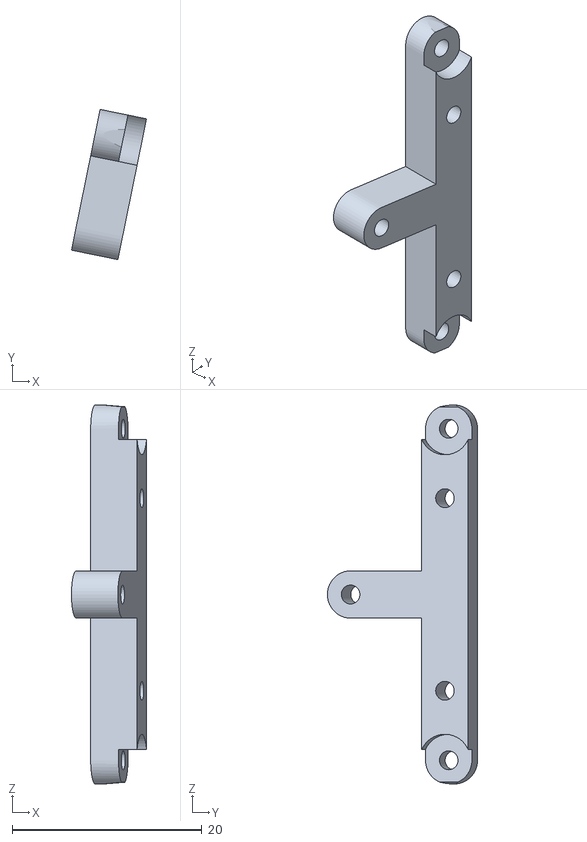
[picture p66: CAD file, 2025-03-08]
Joystick/Righthanded joystick/Head/PCB holder.stl
7.92 x 15.9 x 40.0
