Banjer21/DIY-HOTAS/Joystick/Righthanded joystick/Gimbal/GimbalCase/TopLCP.stl

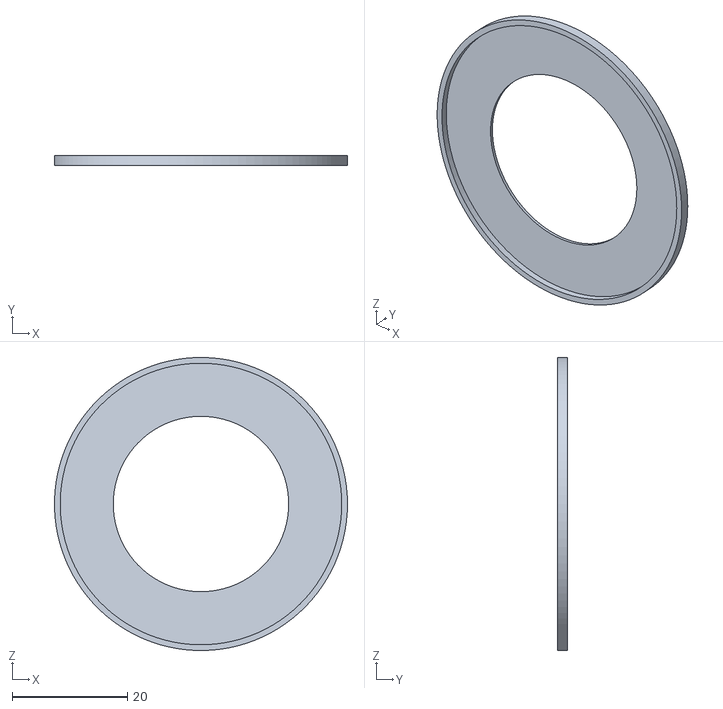
[picture p67: CAD file, 2025-03-08]
Joystick/Righthanded joystick/Gimbal/GimbalCase/TopLCP.stl
50.8 x 1.65 x 50.8
