Banjer21/DIY-HOTAS/Joystick/Righthanded joystick/Gimbal/Xaxis CariageBearing.stl

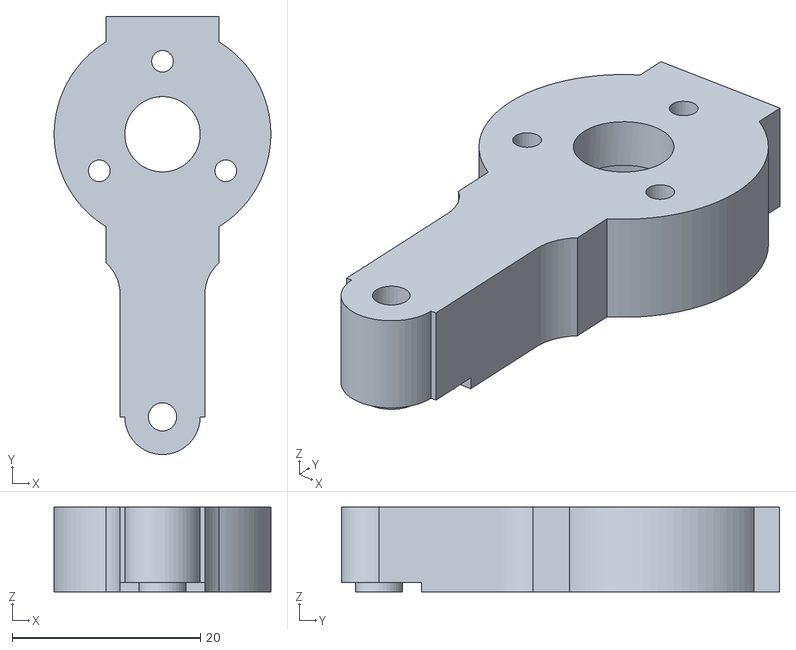
[picture p68: CAD file, 2025-03-08]
Joystick/Righthanded joystick/Gimbal/Xaxis CariageBearing.stl
23.0 x 46.5 x 9.00
