Banjer21/DIY-HOTAS/Joystick/Righthanded joystick/Head/LEDseparator.stl

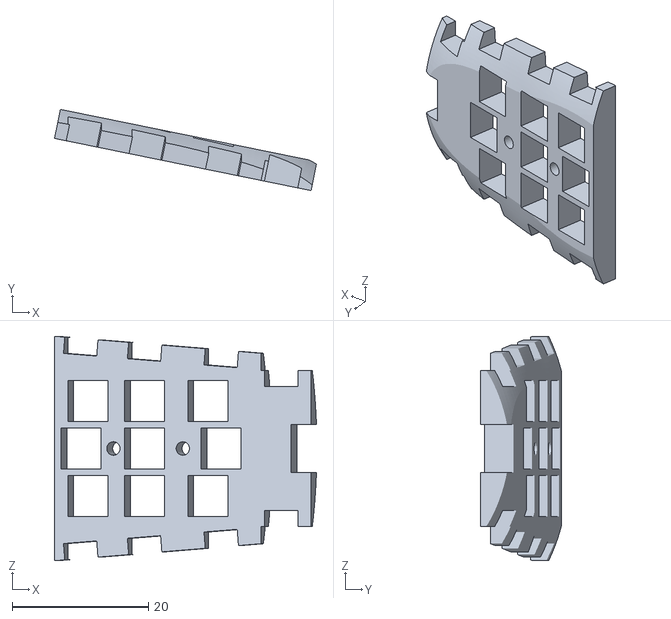
[picture p69: CAD file, 2025-03-08]
Joystick/Righthanded joystick/Head/LEDseparator.stl
38.5 x 11.9 x 33.0
