Banjer21/DIY-HOTAS/Joystick/Righthanded joystick/Head/Right Panel.stl

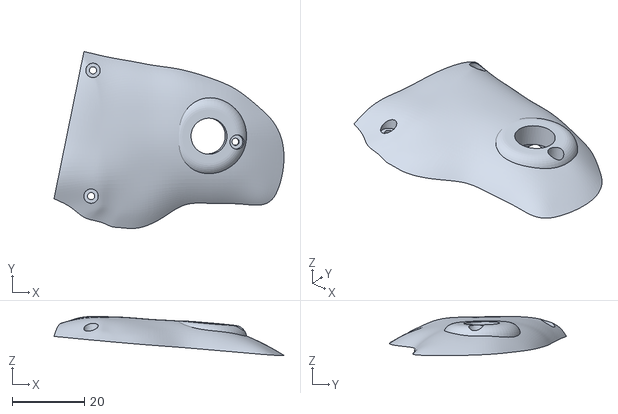
[picture p70: CAD file, 2025-03-08]
Joystick/Righthanded joystick/Head/Right Panel.stl
63.8 x 49.1 x 10.9
