Banjer21/DIY-HOTAS/Joystick/Righthanded joystick/Head/SpringLever.stl

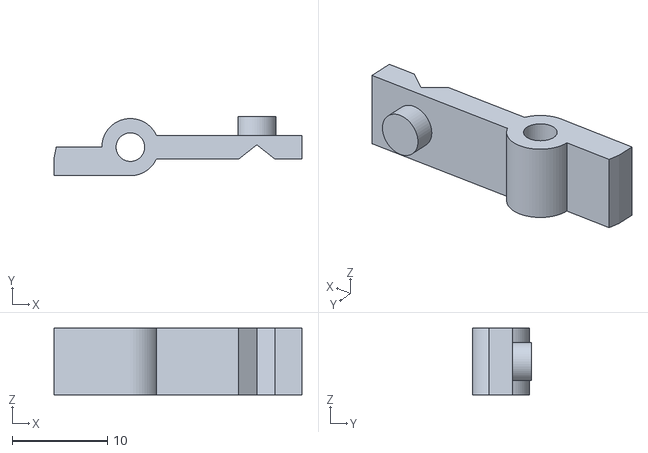
[picture p71: CAD file, 2025-03-08]
Joystick/Righthanded joystick/Head/SpringLever.stl
26.0 x 6.24 x 7.00
