Banjer21/DIY-HOTAS/Joystick/Righthanded joystick/Head/Diffuser Top.stl

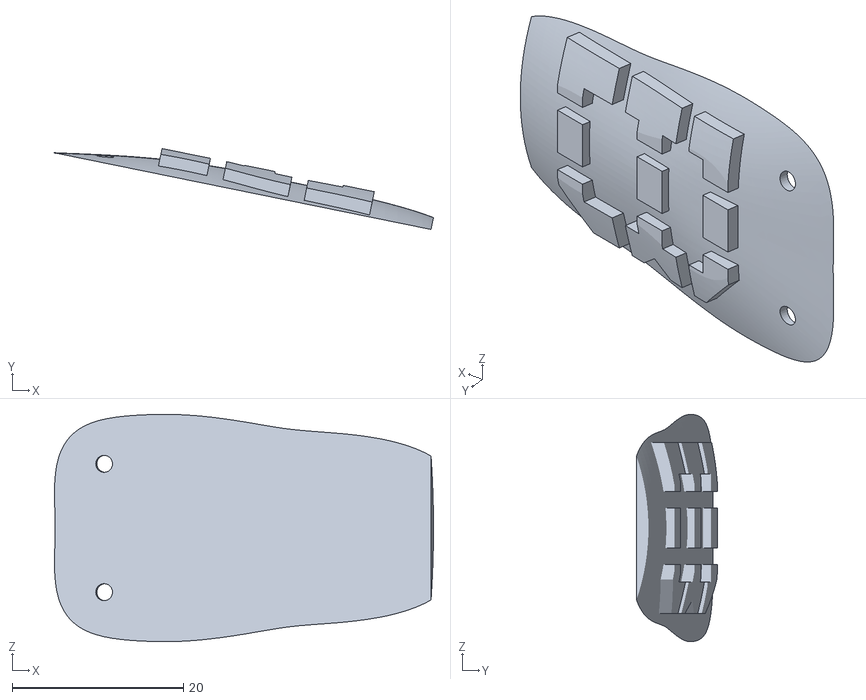
[picture p72: CAD file, 2025-03-08]
Joystick/Righthanded joystick/Head/Diffuser Top.stl
44.3 x 9.46 x 26.6
