Banjer21/DIY-HOTAS/Joystick/Righthanded Updated/Head/DiffuserV3 [B21] [ADD].stl

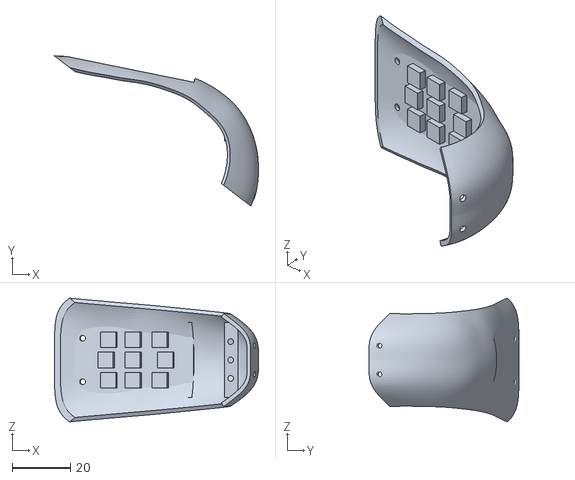
[picture p73: CAD file, 2025-05-15]
Joystick/Righthanded Updated/Head/DiffuserV3 [B21] [ADD].stl
70.3 x 51.7 x 42.6
