Banjer21/DIY-HOTAS/Joystick/Righthanded Updated/Head/Head Body [B21] [ADD].stl

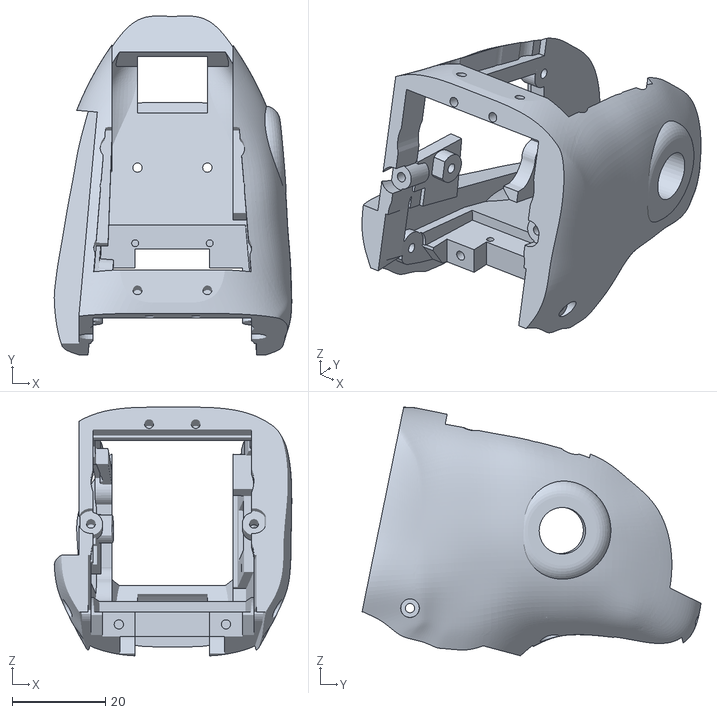
[picture p74: CAD file, 2025-05-15]
Joystick/Righthanded Updated/Head/Head Body [B21] [ADD].stl
51.0 x 72.8 x 53.4
